Mardikas/Balancer/drawings/Printer/Arduino_MPU6050_Mount.STL

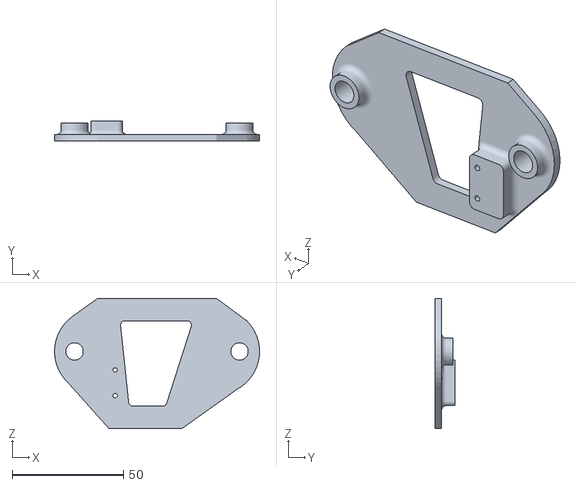
[picture p15: CAD file, 2016-09-13]
drawings/Printer/Arduino_MPU6050_Mount.STL
91.9 x 9.00 x 58.3
