Mardikas/Balancer/drawings/Printer/New_patch/battery_mount_mount.STL

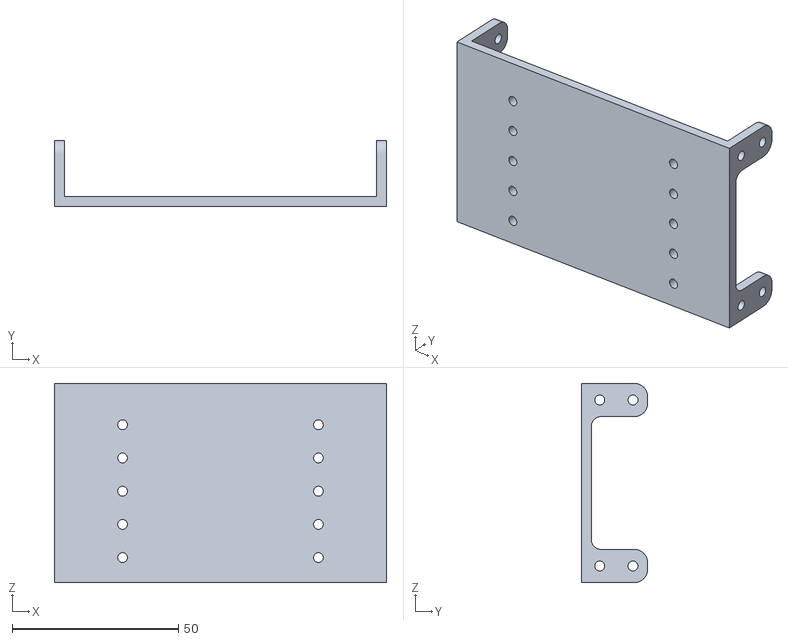
[picture p16: CAD file, 2016-09-27]
drawings/Printer/New_patch/battery_mount_mount.STL
100.0 x 20.0 x 60.0
