Mardikas/Balancer/drawings/Solidworks/Arduino_mount_reviewed.SLDPRT

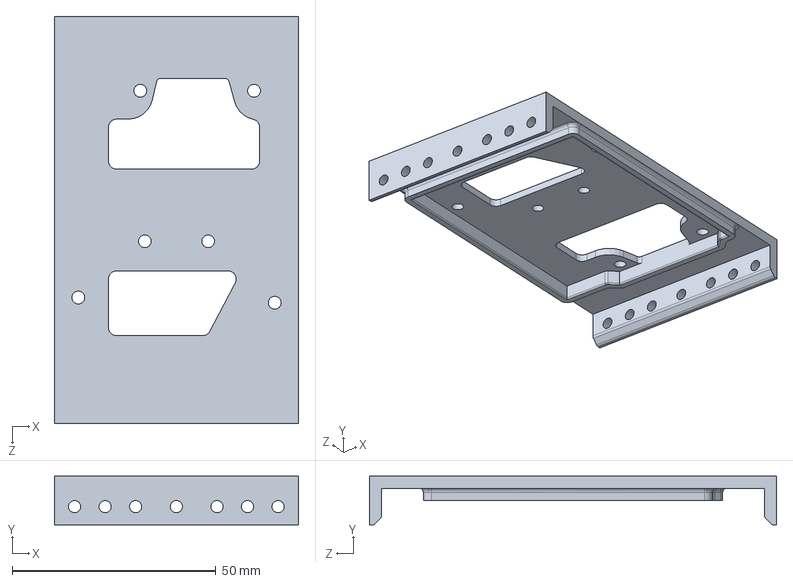
[picture p17: CAD file, 2016-09-27]
drawings/Solidworks/Arduino_mount_reviewed.SLDPRT
60.0 x 12.0 x 100.0 mm
