Mardikas/Balancer/drawings/v2/Arduino Due/Switch - ESwitch - TLE3303.SLDPRT

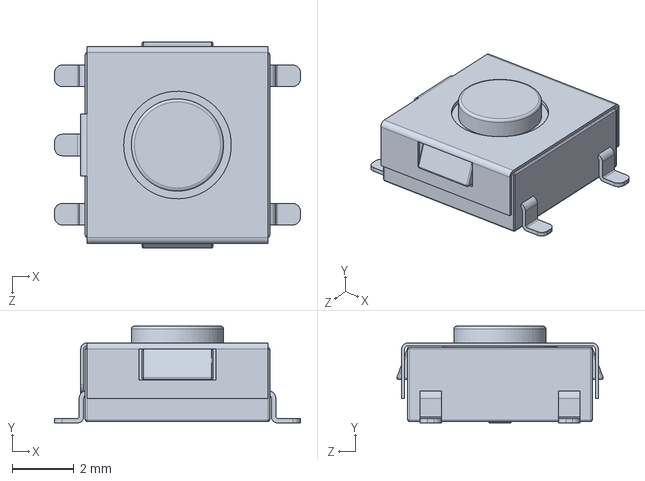
[picture p18: CAD file, 2016-10-29]
drawings/v2/Arduino Due/Switch - ESwitch - TLE3303.SLDPRT
8.00 x 3.15 x 6.71 mm
