Mardikas/Balancer/drawings/v2/arduino-uno-holes.SLDPRT

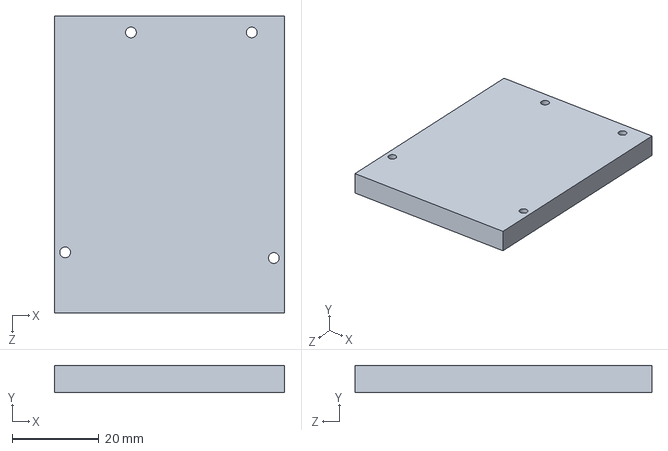
[picture p19: CAD file, 2016-10-29]
drawings/v2/arduino-uno-holes.SLDPRT
53.2 x 6.35 x 68.6 mm
