Mardikas/Balancer/drawings/Printer/Motor_controller_mount.STL

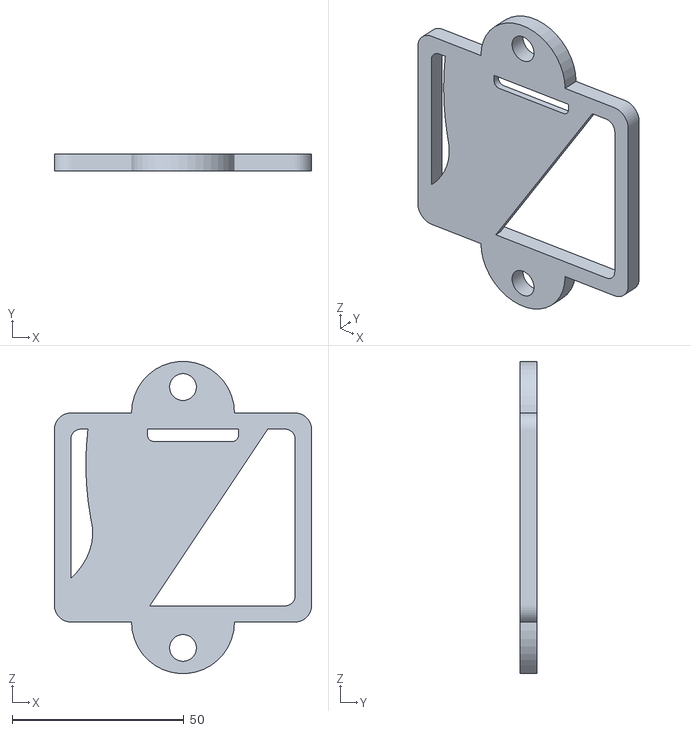
[picture p20: CAD file, 2016-09-13]
drawings/Printer/Motor_controller_mount.STL
75.0 x 5.00 x 90.9
