Mardikas/Balancer/drawings/v2/Arduino Due/Berg Header - 2.54 x 2.SLDPRT

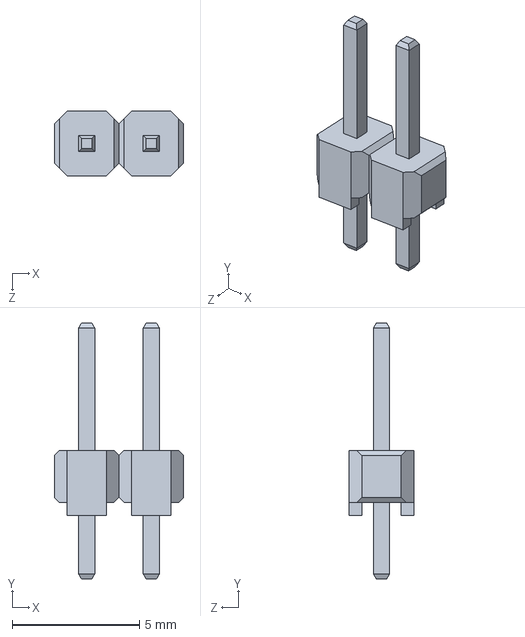
[picture p21: CAD file, 2016-10-29]
drawings/v2/Arduino Due/Berg Header - 2.54 x 2.SLDPRT
5.08 x 10.0 x 2.54 mm
