Mardikas/Balancer/drawings/v2/Horizontal_mount_battery_mount.SLDPRT

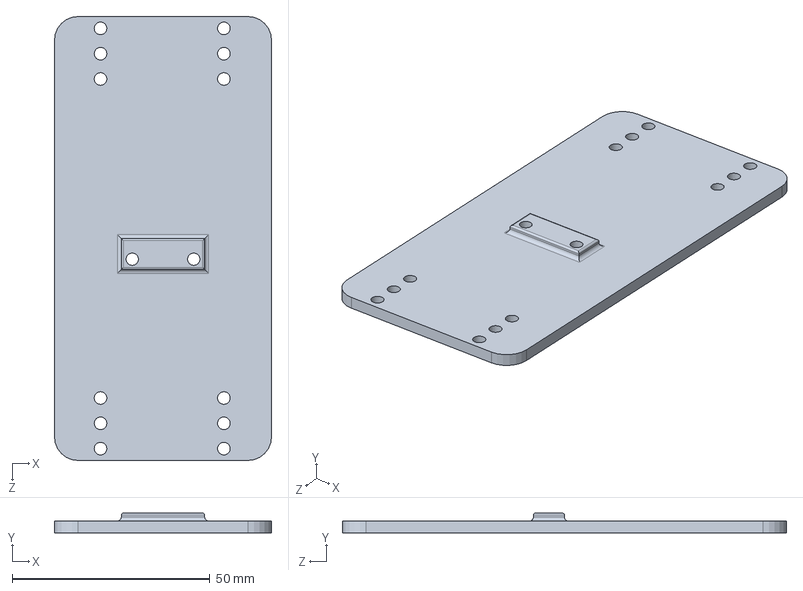
[picture p22: CAD file, 2016-10-29]
drawings/v2/Horizontal_mount_battery_mount.SLDPRT
54.9 x 5.00 x 112.3 mm
