Mardikas/Balancer/drawings/v2/37d-gearmotor-19-30-encoder.step

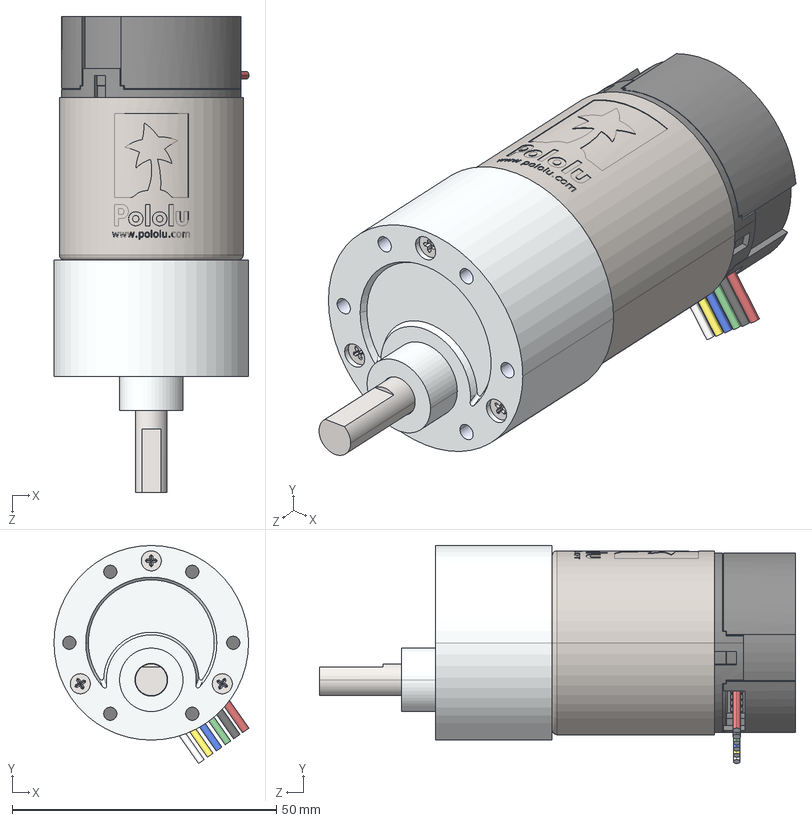
[picture p23: CAD file, 2016-10-29]
drawings/v2/37d-gearmotor-19-30-encoder.step
36.9 x 41.2 x 90.1 mm
