Mardikas/Balancer/drawings/v2/Arduino Due/MicroUSB AB - Hirose - ZX62D-AB-5P8.SLDPRT

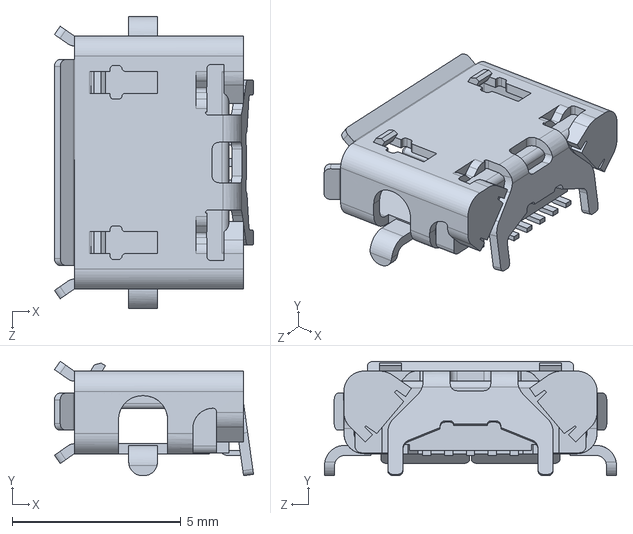
[picture p24: CAD file, 2016-10-29]
drawings/v2/Arduino Due/MicroUSB AB - Hirose - ZX62D-AB-5P8.SLDPRT
5.90 x 3.39 x 8.65 mm
