Mardikas/Balancer/drawings/v2/Arduino Due/Berg Header - 1.27 x 10.SLDPRT

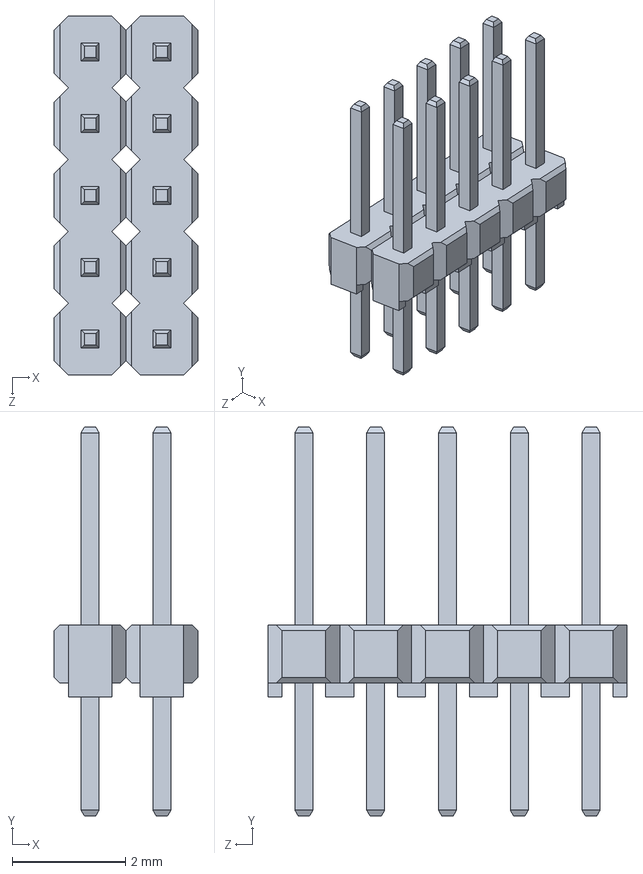
[picture p25: CAD file, 2016-10-29]
drawings/v2/Arduino Due/Berg Header - 1.27 x 10.SLDPRT
2.54 x 6.88 x 6.35 mm
