Mardikas/Balancer/drawings/v2/horizontal_struct_upper.SLDPRT

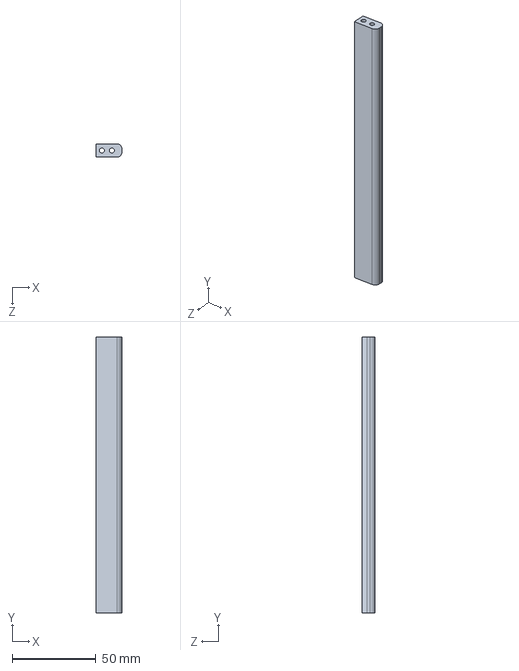
[picture p26: CAD file, 2016-10-29]
drawings/v2/horizontal_struct_upper.SLDPRT
15.5 x 165.0 x 8.00 mm
