Mardikas/Balancer/drawings/Solidworks/motor.SLDPRT

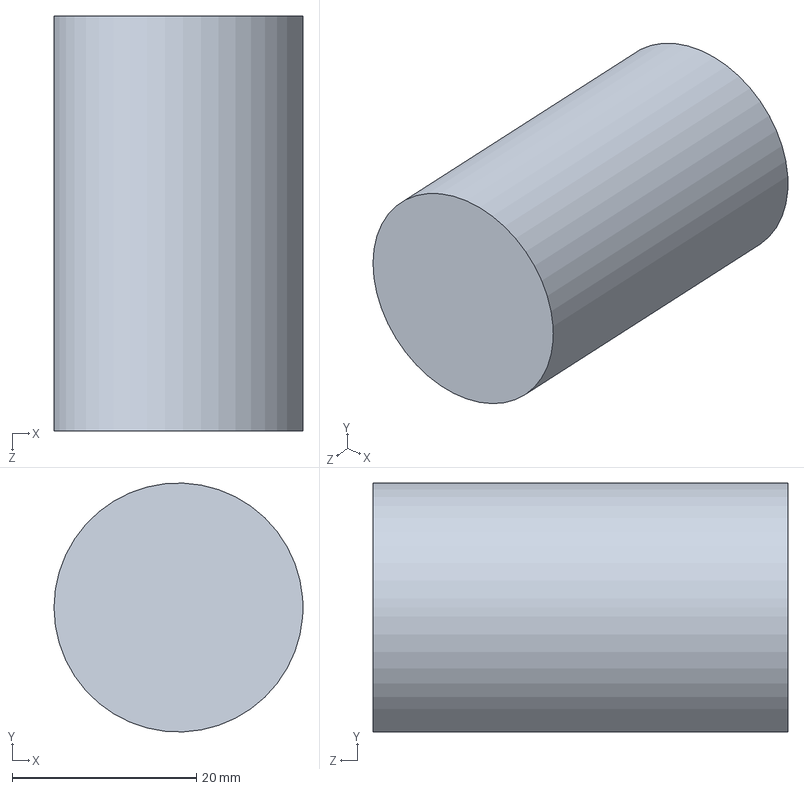
[picture p27: CAD file, 2016-09-27]
drawings/Solidworks/motor.SLDPRT
27.0 x 27.0 x 45.0 mm
