Mardikas/Balancer/drawings/v2/Arduino Due/Berg Header Receptacle 2.54 x 8 - FCI - 66951-008LF.SLDPRT

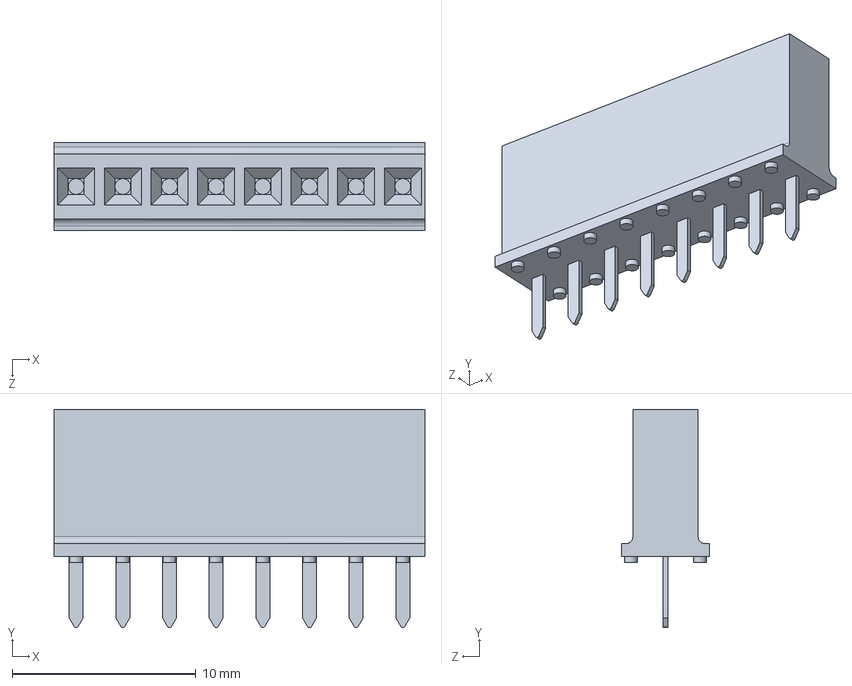
[picture p28: CAD file, 2016-10-29]
drawings/v2/Arduino Due/Berg Header Receptacle 2.54 x 8 - FCI - 66951-008LF.SLDPRT
20.2 x 11.9 x 4.78 mm
