Mardikas/Balancer/drawings/v2/arduino-due-or-mega-holes.SLDPRT

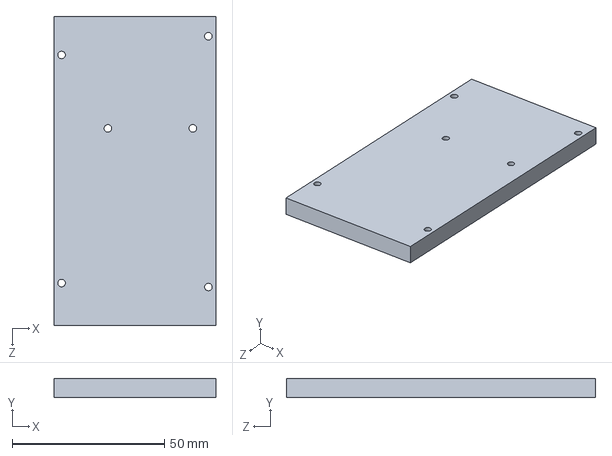
[picture p29: CAD file, 2016-10-29]
drawings/v2/arduino-due-or-mega-holes.SLDPRT
53.2 x 6.35 x 101.6 mm
