Mardikas/Balancer/drawings/v2/Arduino Due/MicroUSB AB - Hirose - ZX62-AB-5PA.SLDPRT

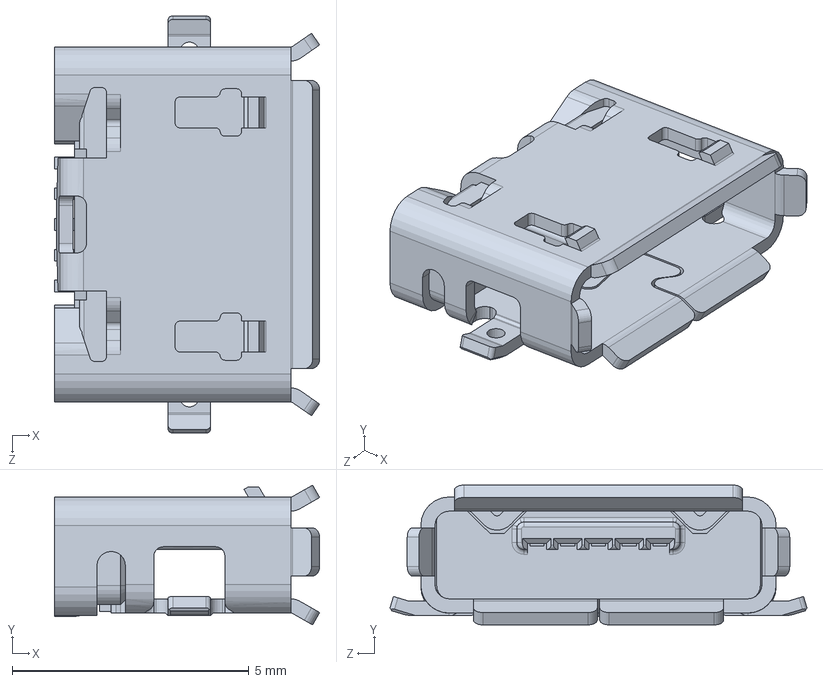
[picture p30: CAD file, 2016-10-29]
drawings/v2/Arduino Due/MicroUSB AB - Hirose - ZX62-AB-5PA.SLDPRT
5.60 x 2.95 x 8.80 mm
