Mardikas/Balancer/drawings/v2/arduino-due or mega-mount-plate.SLDPRT

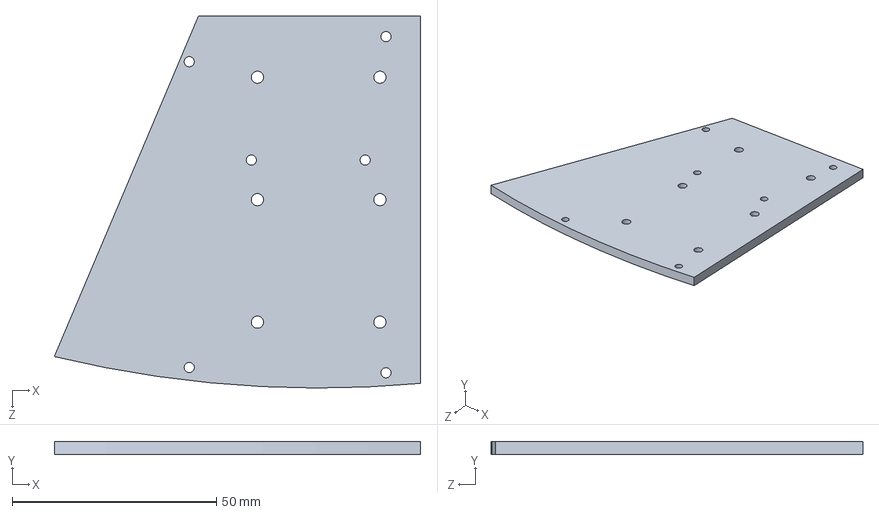
[picture p31: CAD file, 2016-10-29]
drawings/v2/arduino-due or mega-mount-plate.SLDPRT
89.8 x 3.17 x 91.1 mm
