Mardikas/Balancer/drawings/Solidworks/MPU6050_base.SLDPRT

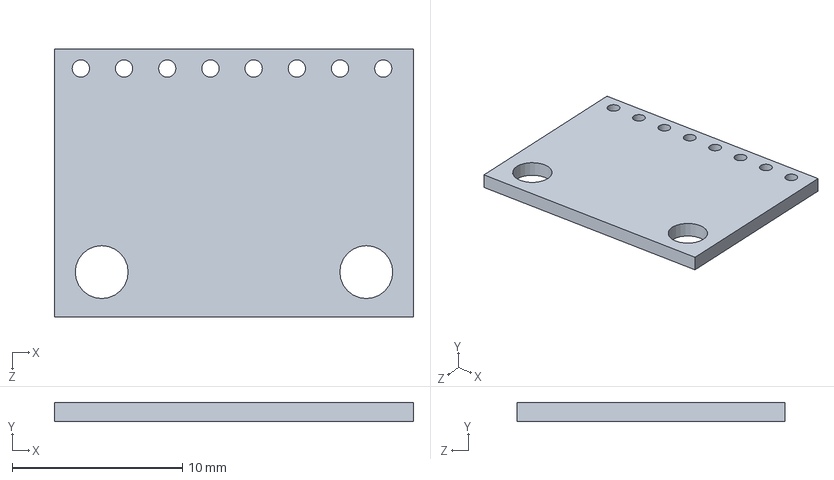
[picture p32: CAD file, 2016-09-27]
drawings/Solidworks/MPU6050_base.SLDPRT
21.1 x 1.14 x 15.7 mm
