Mardikas/Balancer/drawings/v2/Arduino Due/LED - Kingbright - KPT-3216EC.SLDPRT

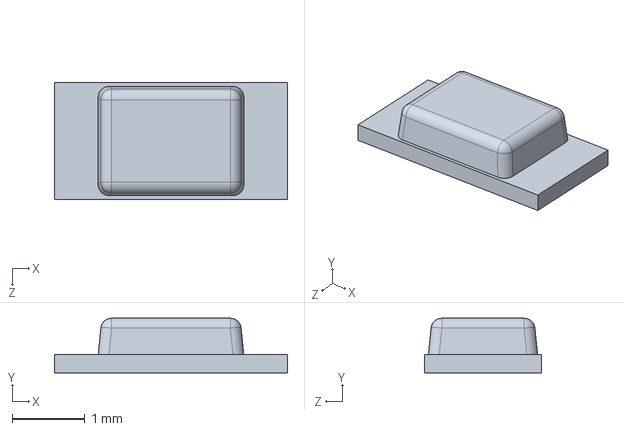
[picture p33: CAD file, 2016-10-29]
drawings/v2/Arduino Due/LED - Kingbright - KPT-3216EC.SLDPRT
3.20 x 0.75 x 1.60 mm
