Mardikas/Balancer/drawings/v2/Arduino_due_mount_wall.SLDPRT

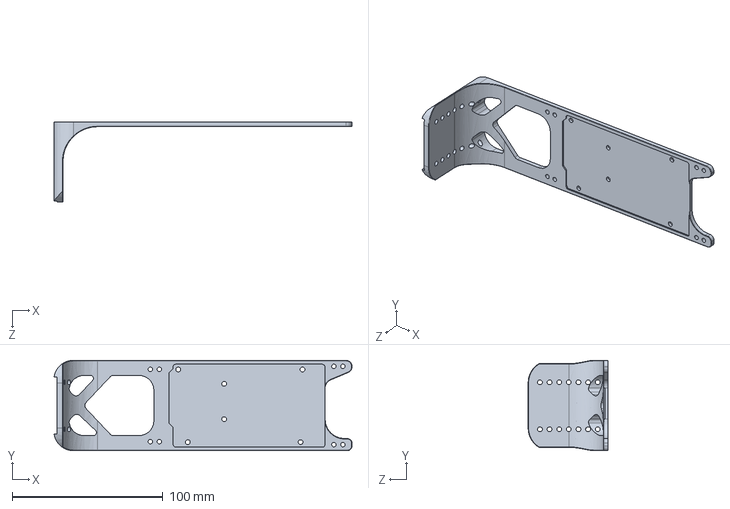
[picture p34: CAD file, 2016-10-29]
drawings/v2/Arduino_due_mount_wall.SLDPRT
198.0 x 60.0 x 53.0 mm
