Mardikas/Balancer/drawings/Solidworks/motor_floor_rod_stabilizer.SLDPRT

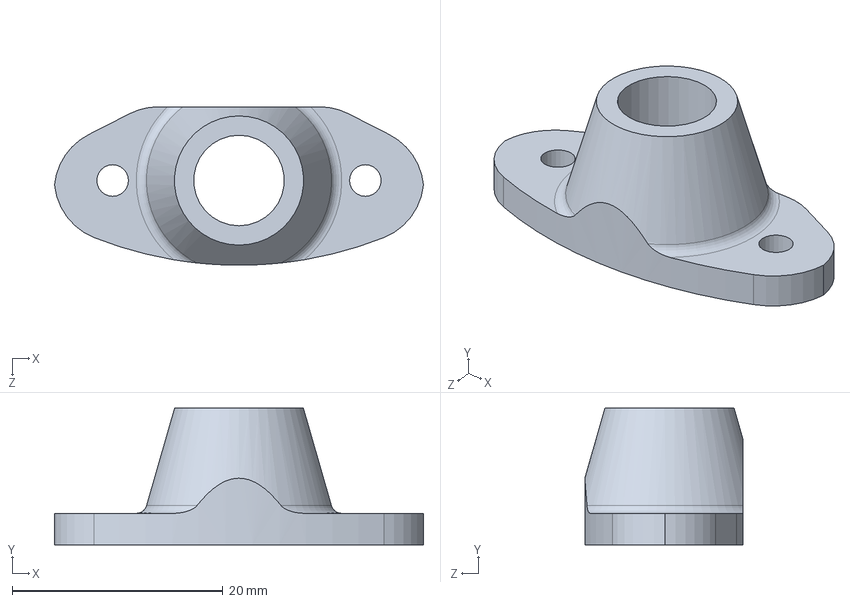
[picture p35: CAD file, 2016-09-27]
drawings/Solidworks/motor_floor_rod_stabilizer.SLDPRT
35.0 x 13.0 x 15.0 mm
