Mardikas/Balancer/drawings/v2/Arduino Due/Capacitor.SLDPRT

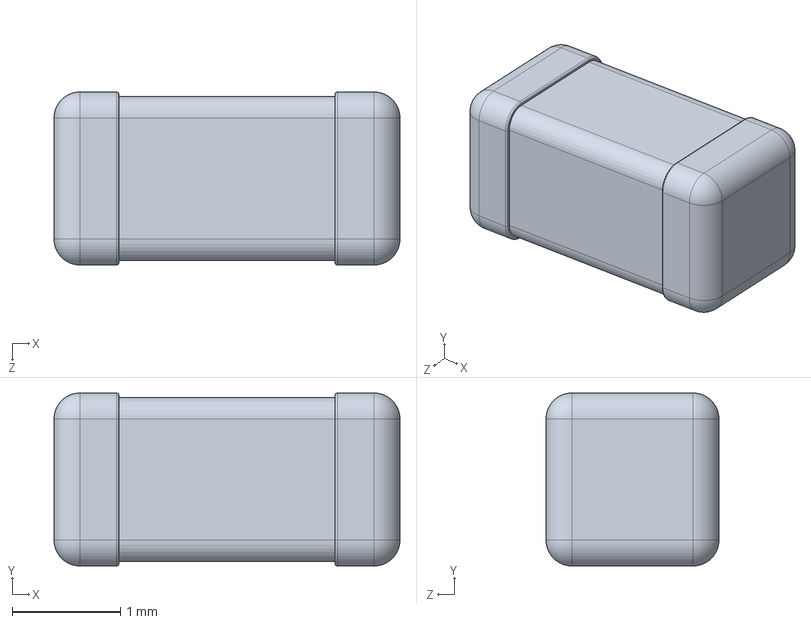
[picture p36: CAD file, 2016-10-29]
drawings/v2/Arduino Due/Capacitor.SLDPRT
3.20 x 1.60 x 1.60 mm
