Mardikas/Balancer/drawings/v2/Motor_controller_mount_wall_.SLDPRT

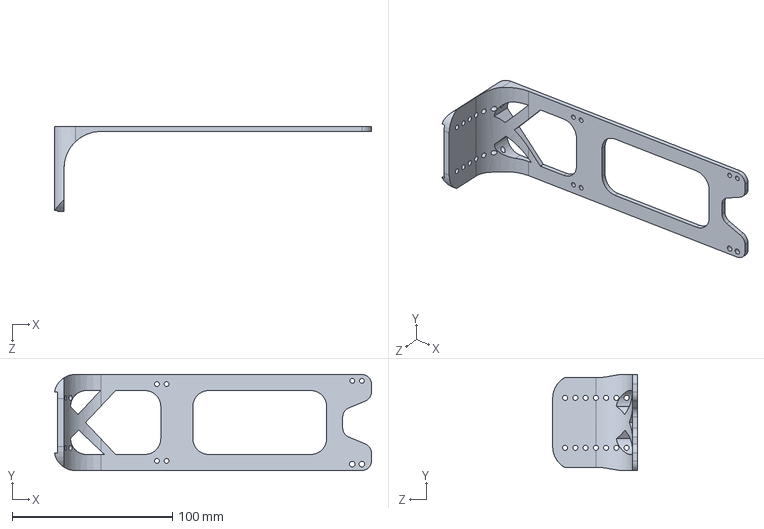
[picture p37: CAD file, 2016-10-29]
drawings/v2/Motor_controller_mount_wall_.SLDPRT
198.0 x 60.0 x 53.0 mm
