Mardikas/Balancer/drawings/v2/Arduino Due/Microchip - Atmel - SAM3X8EAU.SLDPRT

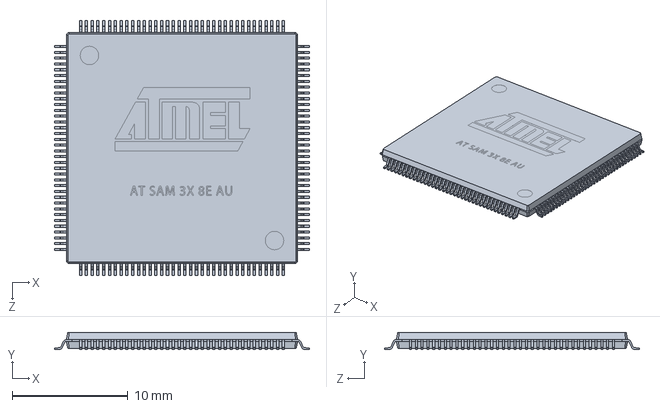
[picture p38: CAD file, 2016-10-29]
drawings/v2/Arduino Due/Microchip - Atmel - SAM3X8EAU.SLDPRT
22.0 x 1.50 x 22.0 mm
