Mardikas/Balancer/drawings/v2/Pololu Stamped Aluminum L-Bracket Pair for 37D mm Metal Gearmotors.SLDPRT

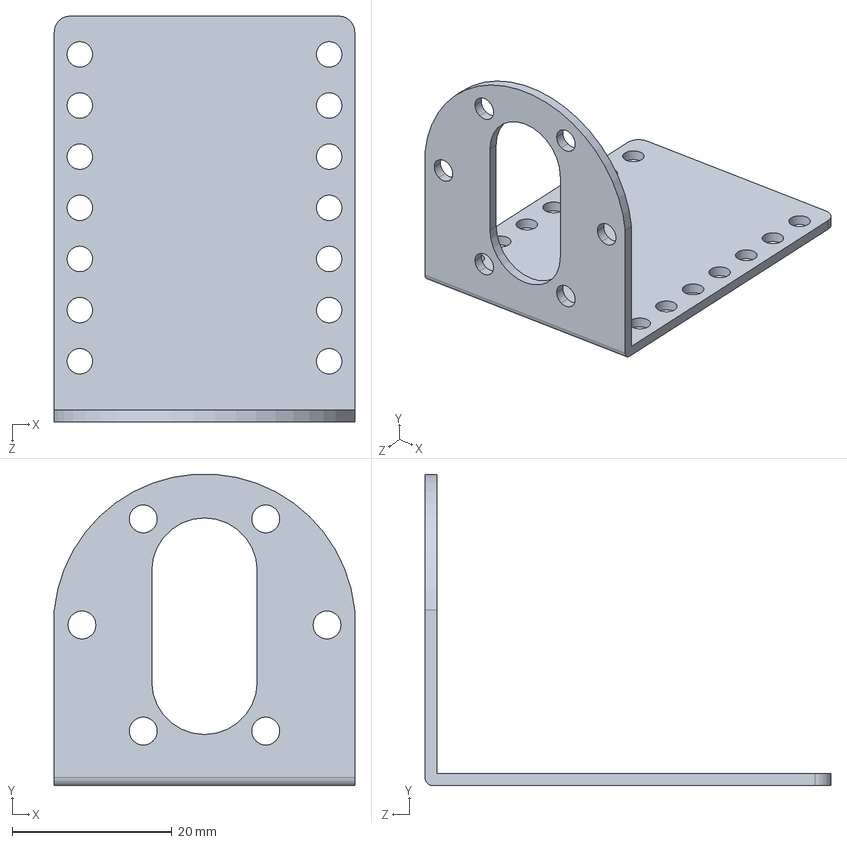
[picture p39: CAD file, 2016-10-29]
drawings/v2/Pololu Stamped Aluminum L-Bracket Pair for 37D mm Metal Gearmotors.SLDPRT
37.6 x 39.0 x 50.8 mm
