Mardikas/Balancer/drawings/v2/Arduino Due/Capacitor - Nichicon - UUR1C101MCL1GS.SLDPRT

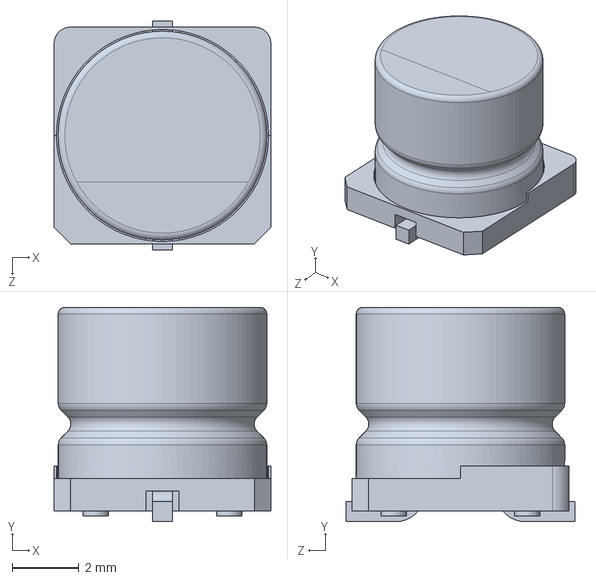
[picture p40: CAD file, 2016-10-29]
drawings/v2/Arduino Due/Capacitor - Nichicon - UUR1C101MCL1GS.SLDPRT
6.50 x 6.42 x 6.85 mm
