Mardikas/Balancer/drawings/v2/Arduino Due/Berg Header Receptacle 2.54 x 36 - FCI - 66953-018LF.SLDPRT

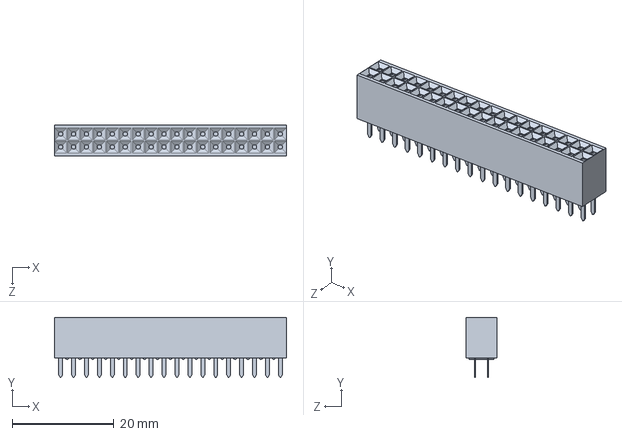
[picture p41: CAD file, 2016-10-29]
drawings/v2/Arduino Due/Berg Header Receptacle 2.54 x 36 - FCI - 66953-018LF.SLDPRT
45.6 x 11.8 x 6.10 mm
