Mardikas/Balancer/drawings/Solidworks/Arduino_MPU6050_Mount.SLDPRT

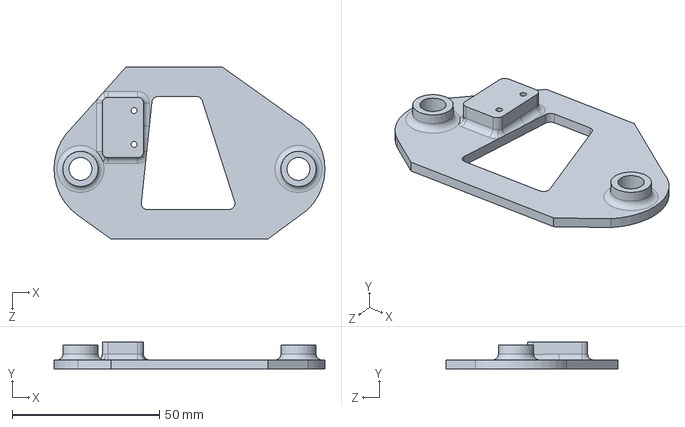
[picture p42: CAD file, 2016-09-13]
drawings/Solidworks/Arduino_MPU6050_Mount.SLDPRT
92.0 x 9.00 x 58.3 mm
