Mardikas/Balancer/drawings/v2/Arduino Due/PCB - Arduino.SLDPRT

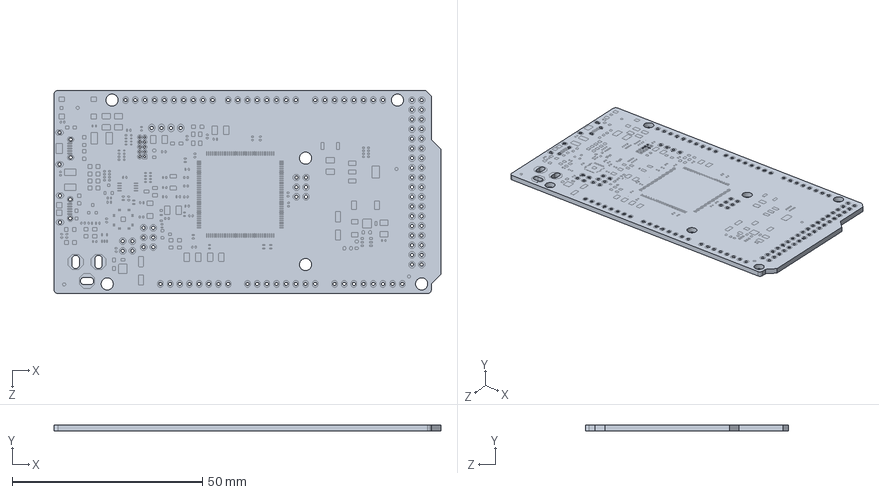
[picture p43: CAD file, 2016-10-29]
drawings/v2/Arduino Due/PCB - Arduino.SLDPRT
101.6 x 1.62 x 53.3 mm
