Mardikas/Balancer/drawings/v2/Arduino Due/MicroUSB B - Hirose - ZX62D-B-5P8.SLDPRT

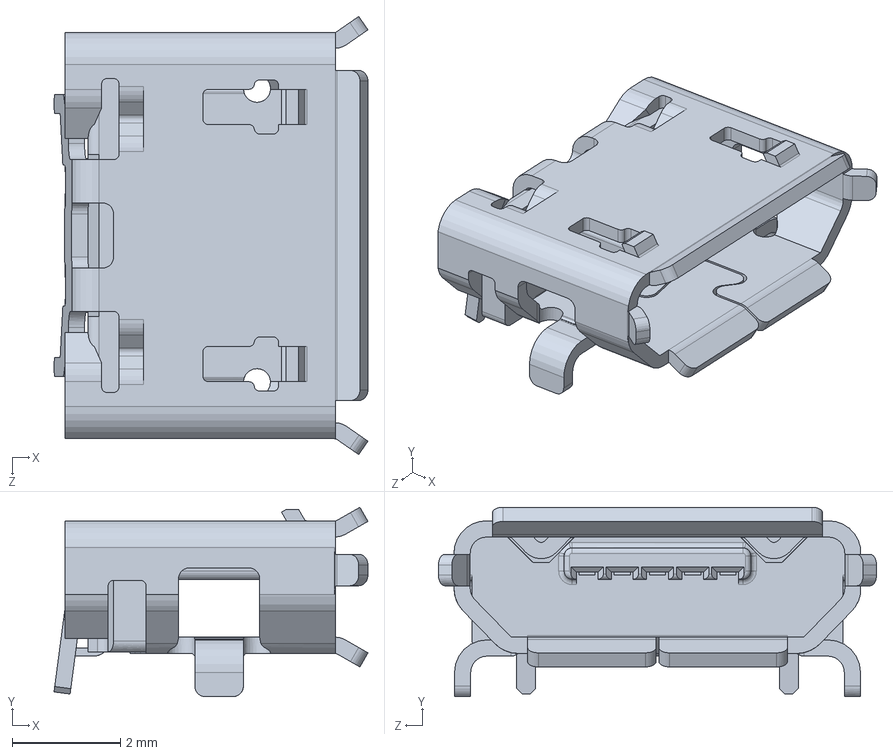
[picture p44: CAD file, 2016-10-29]
drawings/v2/Arduino Due/MicroUSB B - Hirose - ZX62D-B-5P8.SLDPRT
5.80 x 3.50 x 8.09 mm
